jdc-cunningham/camera-jdc34/sughoi.jpeg

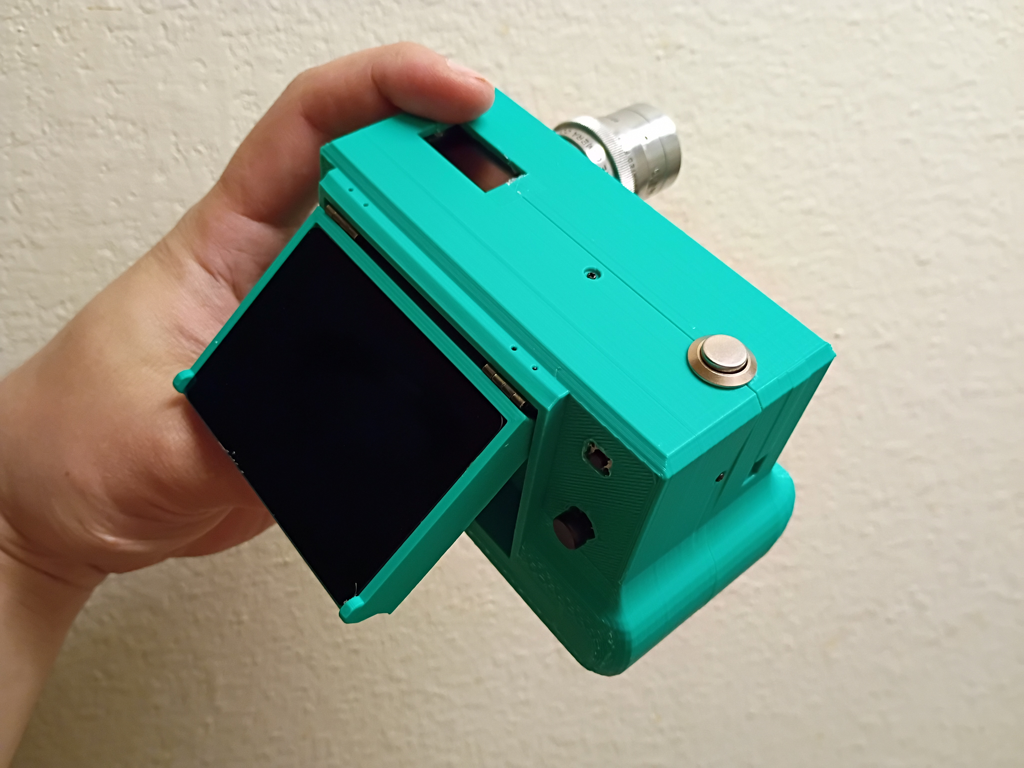
sughoi.jpeg
